leocrini/OraQuadra/IMMAGINI/IMG_9129.jpg

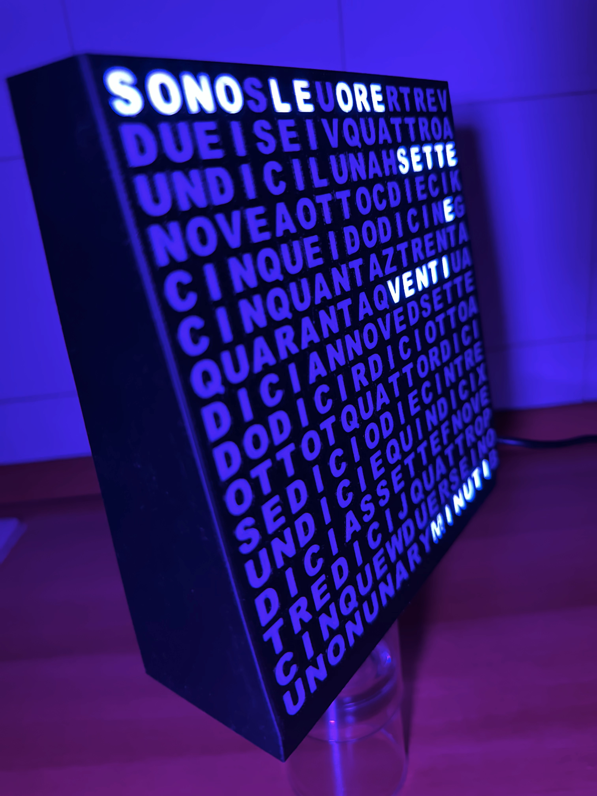
IMMAGINI/IMG_9129.jpg
