leocrini/OraQuadra/IMMAGINI/IMG_9130.jpg

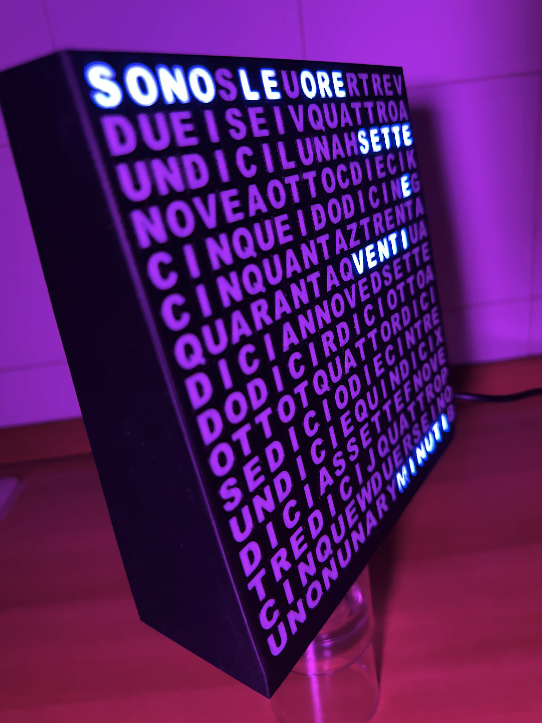
IMMAGINI/IMG_9130.jpg
