leocrini/OraQuadra/IMMAGINI/IMG_9132.jpg

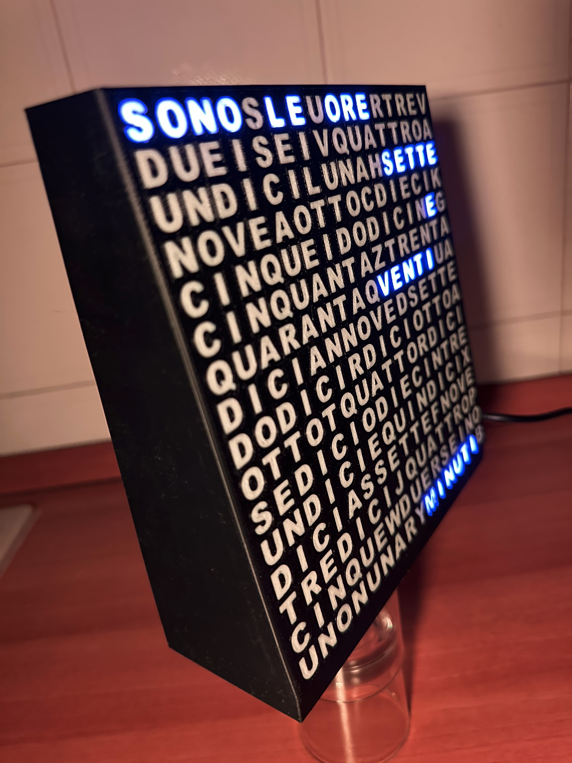
IMMAGINI/IMG_9132.jpg
