leocrini/OraQuadra/IMMAGINI/IMG_9133.jpg

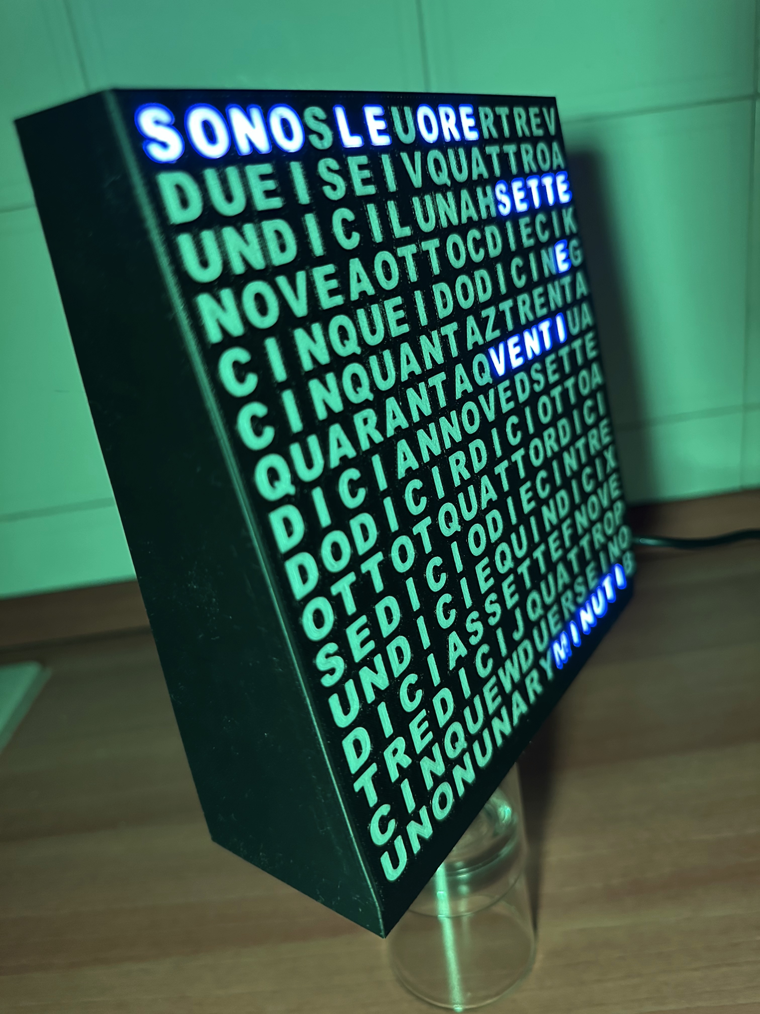
IMMAGINI/IMG_9133.jpg
